brrastak/g031_sht40/firmware/src/bsp.rs

//! Board Support Package: hardware related stuff, like pin configuration, sensor and display initialization, etc.

use cortex_m::singleton;
use embedded_hal_bus::spi::ExclusiveDevice;
use epd_waveshare::epd1in02::Epd1in02;
use hal::{
    gpio::{
        Analog, Input, OpenDrain, Output, PA5, PA7, PB6, PB7, PullDown, PushPull, SignalEdge,
        gpioa, gpioa::PA, gpiob::PB,
    },
    i2c::{Config, I2c},
    pac::{EXTI, I2C1, SPI1, TIM2, TIM3, TIM14, TIM16, TIM17},
    power::{LowPowerMode, PowerMode},
    prelude::*,
    rcc,
    rtc::{Alarm, Event, Rtc},
    spi::{self, Mode, NoMiso, Phase, Polarity, SpiBus},
    time::{Date, Month, MonthDay, Year},
    timer::delay::Delay,
};
use inverted_pin::InvertedPin;
use sht4x::{Precision, Sht4x};
use stm32g0xx_hal as hal;

use crate::data::Data;
pub use crate::display::Display;

type Sht = sht4x::Sht4x<I2c<I2C1, PB7<Output<OpenDrain>>, PB6<Output<OpenDrain>>>, Delay<TIM14>>;
pub type DebugPin = PA<Output<PushPull>>;
// Types for EPD display
pub type EpdDelay = Delay<TIM16>;
pub type EpdSpiDev = ExclusiveDevice<
    SpiBus<SPI1, (PA5<Analog>, NoMiso, PA7<Analog>)>,
    PA<Output<PushPull>>,
    &'static mut Delay<TIM17>,
>;
pub type Epd = Epd1in02<
    EpdSpiDev,
    PA<Input<PullDown>>,
    PA<Output<PushPull>>,
    PA<Output<PushPull>>,
    Delay<TIM16>,
>;

pub struct Sensor {
    sensor: Sht,
    en_sensor: InvertedPin<gpioa::PA<Output<OpenDrain>>>,
    inner_delay: Delay<TIM14>,
    extern_delay: Delay<TIM3>,
}

pub struct Led {
    led: PB<Output<PushPull>>,
    led_delay: Delay<TIM2>,
    pub exti: EXTI,
}

pub struct Board {
    pub display: Display,
    pub sensor: Sensor,
    pub rtc: Rtc,
    pub led: Led,
}

impl Board {
    /// Configure clock to 1MHz,
    /// initialize sensor and display,
    /// configure RTC to wake up every 1 minute,
    /// and set up the board to enter deep-sleep on wfi.
    pub fn new(periph: hal::pac::Peripherals, core: cortex_m::Peripherals) -> Self {
        // Configure clock to 1MHz
        let mut rcc = periph.RCC.freeze(rcc::Config::hsi(rcc::Prescaler::Div16));

        let gpioa = periph.GPIOA.split(&mut rcc);
        let gpiob = periph.GPIOB.split(&mut rcc);

        // Sht40 sensor
        let en_sensor = gpioa
            .pa0
            .into_open_drain_output_in_state(PinState::High)
            .downgrade();
        let en_sensor = InvertedPin::new(en_sensor);
        let sda = gpiob.pb7.into_open_drain_output_in_state(PinState::High);
        let scl = gpiob.pb6.into_open_drain_output_in_state(PinState::High);
        let i2c = periph.I2C1.i2c(sda, scl, Config::new(100.kHz()), &mut rcc);
        let sensor: Sht = Sht4x::new(i2c);
        let inner_delay = periph.TIM14.delay(&mut rcc);
        let extern_delay = periph.TIM3.delay(&mut rcc);

        // LED and button
        let led = gpiob
            .pb9
            .into_push_pull_output_in_state(PinState::Low)
            .downgrade();
        let led_delay = periph.TIM2.delay(&mut rcc);
        let mut exti = periph.EXTI;
        let _button = gpioa.pa1.listen(SignalEdge::Rising, &mut exti);

        // RTC
        let date = Date::new(Year(0), Month(0), MonthDay(0));
        // Every time as seconds value turns 0
        let alarm = Alarm::new().set_seconds(0);
        let mut rtc = periph.RTC.constrain(&mut rcc);
        rtc.set_date(&date);
        rtc.set_alarm_a(alarm);
        rtc.listen(Event::AlarmA);

        // Let the core enter deep-sleep while waiting on wfi
        let mut power = periph.PWR.constrain(&mut rcc);
        power.set_mode(PowerMode::UltraLowPower(LowPowerMode::StopMode2));
        let mut scb = core.SCB;
        scb.set_sleepdeep();

        // Epd display
        let en_epd = gpioa
            .pa4
            .into_push_pull_output_in_state(PinState::High)
            .downgrade();
        let epd_busy = gpioa.pa10.into_pull_down_input().downgrade();
        let epd_reset = gpioa.pa9.into_push_pull_output().downgrade();
        let epd_dc = gpioa.pa8.into_push_pull_output().downgrade();
        let epd_cs = gpioa.pa6.into_push_pull_output().downgrade();
        let spi_clk = gpioa.pa5;
        let spi_mosi = gpioa.pa7;

        let mut spi = periph.SPI1.spi(
            (spi_clk, spi::NoMiso, spi_mosi),
            Mode {
                polarity: Polarity::IdleLow,
                phase: Phase::CaptureOnFirstTransition,
            },
            100.kHz(),
            &mut rcc,
        );
        // Set transmit-only mode
        spi.half_duplex_enable(true);
        spi.half_duplex_output_enable(true);

        let tim17 = periph.TIM17;
        let spi_delay: &'static mut _ =
            singleton!(: hal::timer::delay::Delay<hal::pac::TIM17> = tim17.delay(&mut rcc))
                .unwrap();
        let spi_dev = ExclusiveDevice::new(spi, epd_cs, spi_delay).expect("SpiDevice error");
        let epd_delay = periph.TIM16.delay(&mut rcc);
        let display = Display::new(spi_dev, epd_busy, epd_dc, epd_reset, epd_delay, en_epd, rcc);

        // Initialize hardware components and create SensorSystem and DisplaySystem instances
        let sensor = Sensor {
            sensor,
            en_sensor,
            inner_delay,
            extern_delay,
        };

        let led = Led {
            led,
            led_delay,
            exti,
        };

        Board {
            display,
            sensor,
            rtc,
            led,
        }
    }
}

impl Sensor {
    pub fn read(&mut self) -> Option<Data> {
        self.en_sensor.set_high().ok();
        // Delay after switching sensor on
        self.extern_delay.delay(2.millis());
        let measurement = self.sensor.measure(Precision::High, &mut self.inner_delay);
        self.en_sensor.set_low().ok();

        Data::from_sensor_measurement(measurement)
    }
}

impl Led {
    pub fn blink(&mut self) {
        self.led.set_high().ok();
        self.led_delay.delay(2.millis());
        self.led.set_low().ok();
    }

    pub fn exti_unpend(&mut self) {
        self.exti.unpend(hal::exti::Event::GPIO1);
    }
}
